JayPi4c/SoftSkillsWetterViz/WetterViz/secrets_example.h

// ========================  hier deinen API-Key eintragen!!!  ============================================================================================================
const String OWM_API_KEY = "ACryptyKey"; // dein Open-Weather-Map-API-Schluessel, kostenlos beziehbar ueber https://openweathermap.org/
const char BLYNK_API_KEY[] = "ACryptyKey"; // dein Blynk API Schluessel
const char BLYNK_SERVER[] = "ABlynkyURL"; // die URL zu dem Blynk-Server
const int BLYNK_PORT = 8080; // Port des Blynk-Servers (default: 8080)
const char ssid[] =  "AFancySSID"; // dein SSID (Name des Wlans, mit dem du dich verbindest)
const char pass[] = "ASecretPassword"; // das Passwort für den SSID
// ========================================================================================================================================================================
